juanmb/SkyPointer/python/sky_pointer/pointer.py

from math import pi
from pointing_model import PointingModel
from protocol import Protocol, STEPS
from coords import Coords, EqCoords


def _steps2rad(steps):
    p = 2.*(steps % STEPS)/STEPS
    return pi*(p if p <= 1 else p-2)

def _rad2steps(angle):
    a = (angle/2.) % pi
    return STEPS*(a if a <= pi else pi-a)/pi

def steps2rad(a, b):
    return _steps2rad(a), _steps2rad(b)

def rad2steps(a, b):
    return _rad2steps(a), _rad2steps(b)


class Pointer:
    def __init__(self, device='/dev/ttyUSB0', baud=115200):
        self.__hw = Protocol(device, baud)
        self.hid = self.get_id()
        self.calib = self.__get_calib()
        self.__pm = PointingModel(z1=self.calib[0], z2=self.calib[1],
                                  z3=self.calib[2])
        self.target = EqCoords(0, 0)
        self.home()

    def get_id(self):
        return self.__hw.get_id()

    def home(self):
        return self.__hw.home()

    def __get_calib(self):
        return [self.__hw.get_calib(i) for i in range(3)]

    def set_calib(self, calib):
        if len(calib) != 3:
            raise ValueError("Wrong number of calibration values")

        for i, v in enumerate(calib):
            self.__hw.set_calib(i, v)

    def set_ref(self, eq=None, inst=None, t=0):
        self.__pm.set_ref(eq or self.target, inst or self.get_inst_coords(), t)

    def get_refs(self):
        """Return a list of dictionaries, each containing the observation time,
        equatorial and instrumental coordinates of a reference star"""
        eq = self.__pm.eq_refs
        inst = self.__pm.inst_refs
        t = self.__pm.t_refs

        refs = []
        for i in range(self.__pm.get_nrefs()):
            refs.append({'eq': eq[i], 'inst': inst[i], 't': t[i]})
        return refs

    def steps(self, ha, el):
        self.__hw.move(ha, el)

    def run(self, ha_dir, el_dir):
        if not -1 <= ha_dir <= 1:
            raise ValueError("ha_dir must be between -1 and 1")
        if not -1 <= el_dir <= 1:
            raise ValueError("el_dir must be between -1 and 1")
        half = STEPS/2 - 1
        self.__hw.move(ha_dir*half, el_dir*half)

    def stop(self):
        self.__hw.stop()

    def enable_laser(self, enable):
        self.__hw.enable_laser(enable)

    def get_coords(self):
        return self.__pm.inst_to_eq(steps2rad(*self.__hw.get_pos()))

    def get_inst_coords(self):
        return Coords(*steps2rad(*self.__hw.get_pos()))

    def get_motor_pos(self):
        return self.__hw.get_pos()

    def goto(self, eq):
        self.target = eq
        self.__hw.goto(*rad2steps(*self.__pm.eq_to_inst(eq)))

    def close(self):
        self.__hw.close()
