juanmb/SkyPointer/python/sky_pointer/gui/bright_stars.py

bright_stars = [
    ('Alpha Canis Majoris', 'Sirius', 1.76715, -0.29147),
    ('Alpha Carinae', 'Canopus', 1.67552, -0.91979),
    ('Alpha Centauri', 'Rigil Kentaurus', 3.83972, -1.06116),
    ('Alpha Bootis', 'Arcturus', 3.73500, 0.33510),
    ('Alpha Lyrae', 'Vega', 4.87383, 0.67719),
    ('Alpha Aurigae', 'Capella', 1.38317, 0.80285),
    ('Beta Orionis', 'Rigel', 1.37445, -0.14312),
    ('Alpha Canis Minoris', 'Procyon', 2.00277, 0.09076),
    ('Alpha Eridani', 'Achernar', 0.42761, -0.99833),
    ('Alpha Orionis', 'Betelgeuse', 1.54898, 0.12915),
    ('Beta Centauri', 'Hadar', 3.68264, -1.05418),
    ('Alpha Aquilae', 'Altair', 5.19672, 0.15533),
    ('Alpha Crucis', 'Acrux', 3.25940, -1.10130),
    ('Alpha Tauri', 'Aldebaran', 1.20428, 0.28798),
    ('Alpha Scorpii', 'Antares', 4.31533, -0.46077),
    ('Alpha Virginis', 'Spica', 3.51248, -0.19548),
    ('Beta Geminorum', 'Pollux', 2.02895, 0.48869),
    ('Alpha Piscis Austrini', 'Fomalhaut', 6.01266, -0.51662),
    ('Alpha Cygni', 'Deneb', 5.41488, 0.79063),
    ('Beta Crucis', 'Mimosa', 3.35103, -1.04196),
    ('Alpha Leonis', 'Regulus', 2.65290, 0.20944),
    ('Epsilon Canis Majoris', 'Adhara', 1.82823, -0.50615),
    ('Alpha Geminorum', 'Castor', 1.98531, 0.55676),
    ('Lambda Scorpii', 'Shaula', 4.59894, -0.64752),
    ('Gamma Crucis', 'Gacrux', 3.27686, -0.99658),
    ('Gamma Orionis', 'Bellatrix', 1.41808, 0.10996),
    ('Beta Tauri', 'Elnath', 1.42244, 0.49916),
    ('Beta Carinae', 'Miaplacidus', 2.41292, -1.21649),
    ('Epsilon Orionis', 'Alnilam', 1.46608, -0.02094),
    ('Alpha Gruis', 'Alnair', 5.79449, -0.82030),
    ('Zeta Orionis', 'Alnitak', 1.48789, -0.03316),
    ('Epsilon Ursae Majoris', 'Alioth', 3.37721, 0.97738),
    ('Alpha Persei', 'Mirfak', 0.89012, 0.87092),
    ('Alpha Ursae Majoris', 'Dubhe', 2.89725, 1.07861),
    ('Gamma Velorum', 'Regor', 2.13803, -0.82554),
    ('Delta Canis Majoris', 'Wezen', 1.86750, -0.46077),
    ('Epsilon Sagittarii', 'Kaus Australis', 4.81711, -0.60039),
    ('Eta Ursae Majoris', 'Alkaid', 3.61283, 0.86045),
    ('Theta Scorpii', 'Sargas', 4.61203, -0.75049),
    ('Epsilon Carinae', 'Avior', 2.19475, -1.03847),
    ('Beta Aurigae', 'Menkalinan', 1.57080, 0.78365),
    ('Alpha Trianguli Australis', 'Atria', 4.40259, -1.20428),
    ('Gamma Geminorum', 'Alhena', 1.73660, 0.28623),
    ('Alpha Pavonis', 'Peacock', 5.34943, -0.98960),
    ('Delta Velorum', 'Koo She', 2.29074, -0.95470),
    ('Beta Canis Majoris', 'Mirzam', 1.67115, -0.31416),
    ('Alpha Hydrae', 'Alphard', 2.47837, -0.15184),
    ('Alpha Ursae Minoris', 'Polaris', 0.66323, 1.55858),
    ('Gamma Leonis', 'Algieba', 2.70526, 0.34558),
    ('Alpha Arietis', 'Hamal', 0.55414, 0.41015),
    ('Beta Ceti', 'Diphda', 0.19199, -0.31416),
    ('Sigma Sagittarii', 'Nunki', 4.95237, -0.45902),
    ('Theta Centauri', 'Menkent', 3.69573, -0.63530),
    ('Alpha Andromedae', 'Alpheratz', 0.03491, 0.50789),
    ('Beta Andromedae', 'Mirach', 0.30543, 0.62134),
    ('Kappa Orionis', 'Saiph', 1.51844, -0.16930),
    ('Beta Ursae Minoris', 'Kochab', 3.88772, 1.29503),
    ('Beta Gruis', 'Al Dhanab', 5.94721, -0.81856),
    ('Alpha Ophiuchi', 'Rasalhague', 4.60331, 0.21991),
    ('Beta Persei', 'Algol', 0.82030, 0.71558),
    ('Gamma Andromedae', 'Almach', 0.54105, 0.73827),
    ('Beta Leonis', 'Denebola', 3.09360, 0.25482),
    ('Gamma Cassiopeiae', 'Cih', 0.24871, 1.05941),
    ('Gamma Centauri', 'Muhlifain', 3.32485, -0.85521),
    ('Zeta Puppis', 'Naos', 2.11185, -0.69813),
    ('Iota Carinae', 'Aspidiske', 2.43037, -1.03498),
    ('Alpha Coronae Borealis', 'Alphecca', 4.07971, 0.46600),
    ('Lambda Velorum', 'Suhail', 2.39110, -0.75747),
    ('Zeta Ursae Majoris', 'Mizar', 3.50811, 0.95819),
    ('Gamma Cygni', 'Sadr', 5.33198, 0.70337),
    ('Alpha Cassiopeiae', 'Schedar', 0.17890, 0.98611),
    ('Gamma Draconis', 'Eltanin', 4.69930, 0.89884),
    ('Delta Orionis', 'Mintaka', 1.44862, -0.00524),
    ('Beta Cassiopeiae', 'Caph', 0.03927, 1.03323),
    ('Epsilon Centauri', '', 3.57792, -0.93375),
    ('Delta Scorpii', 'Dschubba', 4.18879, -0.39444),
    ('Epsilon Scorpii', 'Wei', 4.40696, -0.59865),
    ('Alpha Lupi', 'Men', 3.84845, -0.82729),
    ('Eta Centauri', '', 3.82227, -0.73653),
    ('Beta Ursae Majoris', 'Merak', 2.88852, 0.98437),
    ('Epsilon Bootis', 'Izar', 3.86154, 0.47298),
    ('Epsilon Pegasi', 'Enif', 5.68977, 0.17279),
    ('Kappa Scorpii', 'Girtab', 4.63385, -0.68068),
    ('Alpha Phoenicis', 'Ankaa', 0.11345, -0.73827),
    ('Gamma Ursae Majoris', 'Phecda', 3.11541, 0.93724),
    ('Eta Ophiuchi', 'Sabik', 4.49422, -0.27402),
    ('Beta Pegasi', 'Scheat', 6.03884, 0.49044),
    ('Eta Canis Majoris', 'Aludra', 1.93732, -0.51138),
    ('Alpha Cephei', 'Alderamin', 5.58069, 1.09258),
    ('Kappa Velorum', 'Markeb', 2.45219, -0.95993),
    ('Epsilon Cygni', 'Gienah', 5.43670, 0.59341),
    ('Alpha Pegasi', 'Markab', 6.04320, 0.26529),
    ('Alpha Ceti', 'Menkar', 0.79412, 0.07156),
    ('Zeta Ophiuchi', 'Han', 4.35023, -0.18500),
    ('Zeta Centauri', 'Al Nair al Kent.', 3.64774, -0.82554),
    ('Delta Leonis', 'Zosma', 2.94088, 0.35779),
    ('Beta Scorpii', 'Graffias', 4.21061, -0.34558),
    ('Alpha Leporis', 'Arneb', 1.45299, -0.31067),
    ('Delta Centauri', '', 3.17650, -0.88488),
    ('Gamma Corvi', 'Gienah Ghurab', 3.21141, -0.30543),
    ('Zeta Sagittarii', 'Ascella', 4.98728, -0.52185),
    ('Beta Librae', 'Zubeneschamali', 4.00117, -0.16406),
    ('Alpha Serpentis', 'Unukalhai', 4.11898, 0.11170),
    ('Beta Arietis', 'Sheratan', 0.50178, 0.36303),
    ('Alpha Librae', 'Zubenelgenubi', 3.88772, -0.27925),
    ('Alpha Columbae', 'Phact', 1.48353, -0.59516),
    ('Theta Aurigae', '', 1.57080, 0.64926),
    ('Beta Corvi', 'Kraz', 3.28995, -0.40841),
    ('Delta Cassiopeiae', 'Ruchbah', 0.37525, 1.05069),
    ('Eta Bootis', 'Muphrid', 3.64337, 0.32114),
    ('Beta Lupi', 'Ke Kouan', 3.92263, -0.75224),
    ('Iota Aurigae', 'Hassaleh', 1.29591, 0.57945),
    ('Mu Velorum', '', 2.82307, -0.86219),
    ('Alpha Muscae', '', 3.30304, -1.20602),
    ('Upsilon Scorpii', 'Lesath', 4.58585, -0.65101),
    ('Pi Puppis', '', 1.90677, -0.64752),
    ('Delta Sagittarii', 'Kaus Meridionalis', 4.80402, -0.52011),
    ('Gamma Aquilae', 'Tarazed', 5.17490, 0.18500),
    ('Delta Ophiuchi', 'Yed Prior', 4.24988, -0.06458),
    ('Eta Draconis', 'Aldhibain', 4.29351, 1.07338),
    ('Theta Carinae', '', 2.80562, -1.12399),
    ('Gamma Virginis', 'Porrima', 3.32485, -0.02618),
    ('Iota Orionis', 'Hatysa', 1.46171, -0.10297),
    ('Iota Centauri', '', 3.49502, -0.64054),
    ('Beta Ophiuchi', 'Cebalrai', 4.63821, 0.08029),
    ('Beta Eridani', 'Kursa', 1.34390, -0.08901),
    ('Beta Herculis', 'Kornephoros', 4.31969, 0.37525),
    ('Delta Crucis', '', 3.20704, -1.02451),
    ('Beta Draconis', 'Rastaban', 4.58149, 0.91281),
    ('Alpha Canum Venaticorum', 'Cor Caroli', 3.38594, 0.66846),
    ('Gamma Lupi', '', 4.07971, -0.71908),
    ('Beta Leporis', 'Nihal', 1.43117, -0.36303),
    ('Zeta Herculis', 'Rutilicus', 4.36769, 0.55152),
    ('Beta Hydri', '', 0.11345, -1.34914),
    ('Tau Scorpii', '', 4.34587, -0.49218),
    ('Lambda Sagittarii', 'Kaus Borealis', 4.83456, -0.44331),
    ('Gamma Pegasi', 'Algenib', 0.05672, 0.26529),
    ('Rho Puppis', 'Turais', 2.12930, -0.42412),
    ('Beta Trianguli Australis', '', 4.16697, -1.10654),
    ('Zeta Persei', '', 1.02102, 0.55676),
    ('Beta Arae', '', 4.55967, -0.96866),
    ('Alpha Arae', 'Choo', 4.59022, -0.87092),
    ('Eta Tauri', 'Alcyone', 0.99047, 0.42062),
    ('Epsilon Virginis', 'Vindemiatrix', 3.41212, 0.19199),
    ('Delta Capricorni', 'Deneb Algedi', 5.70286, -0.28100),
    ('Alpha Hydri', 'Head of Hydrus', 0.51924, -1.07512),
    ('Delta Cygni', '', 5.17054, 0.78714),
    ('Mu Geminorum', 'Tejat', 1.67115, 0.39270),
    ('Gamma Trianguli Australis', '', 4.00989, -1.19904),
    ('Alpha Tucanae', '', 5.84249, -1.05243),
    ('Theta Eridani', 'Acamar', 0.77667, -0.70337),
    ('Pi Sagittarii', 'Albaldah', 5.01782, -0.36652),
    ('Beta Canis Minoris', 'Gomeisa', 1.95041, 0.14486),
    ('Pi Scorpii', '', 4.18443, -0.45553),
    ('Epsilon Persei', '', 1.03847, 0.69813),
    ('Sigma Scorpii', 'Alniyat', 4.28042, -0.44680),
    ('Beta Cygni', 'Albireo', 5.10945, 0.48869),
    ('Beta Aquarii', 'Sadalsuud', 5.63741, -0.09774),
    ('Gamma Persei', '', 0.80721, 0.93375),
    ('Upsilon Carinae', '', 2.56127, -1.13621),
    ('Eta Pegasi', 'Matar', 5.94721, 0.52709),
    ('Tau Puppis', '', 1.78896, -0.88314),
    ('Delta Corvi', 'Algorel', 3.27249, -0.28798),
    ('Alpha Aquarii', 'Sadalmelik', 5.78577, -0.00524),
    ('Gamma Eridani', 'Zaurak', 1.03847, -0.23562),
    ('Zeta Tauri', 'Alheka', 1.47480, 0.36826),
    ('Epsilon Leonis', 'Ras Elased Austr.', 2.55691, 0.41539),
    ('Gamma Sagittarii', 'Alnasl', 4.73857, -0.53058),
    ('Gamma Hydrae', '', 3.48630, -0.40492),
    ('Iota Scorpii', '', 4.66003, -0.69988),
    ('Zeta Aquilae', 'Deneb el Okab', 4.99600, 0.24260),
    ('Beta Trianguli', '', 0.56723, 0.61087),
    ('Psi Ursae Majoris', '', 2.92343, 0.77667),
    ('Gamma Ursae Minoris', 'Pherkad Major', 4.01862, 1.25315),
    ('Mu Scorpii', '', 4.41568, -0.66323),
    ('Gamma Gruis', '', 5.73341, -0.65275),
    ('Delta Persei', '', 0.97302, 0.83427),
    ('Zeta Canis Majoris', 'Phurad', 1.65806, -0.52534),
    ('Omicron Canis Majoris', '', 1.84569, -0.41539),
    ('Epsilon Corvi', 'Minkar', 3.18523, -0.39444),
    ('Epsilon Aurigae', 'Almaaz', 1.31772, 0.76445),
    ('Beta Muscae', '', 3.34231, -1.18857),
    ('Gamma Bootis', 'Seginus', 3.80482, 0.66846),
    ('Beta Capricorni', 'Dabih', 5.32762, -0.25831),
    ('Epsilon Geminorum', 'Mebsuta', 1.76278, 0.43808),
    ('Mu Ursae Majoris', 'Tania Australis', 2.71399, 0.72431),
    ('Delta Draconis', 'Tais', 5.03091, 1.18159),
    ('Eta Sagittarii', '', 4.79093, -0.64228),
    ('Zeta Hydrae', '', 2.33438, 0.10297),
    ('Nu Hydrae', '', 2.83616, -0.28274),
    ('Lambda Centauri', '', 3.03687, -1.09956),
    ('Alpha Indi', 'Persian', 5.40179, -0.82554),
    ('Beta Columbae', 'Wazn', 1.53153, -0.62483),
    ('Iota Ursae Majoris', 'Talita', 2.35183, 0.83776),
    ('Zeta Arae', '', 4.44623, -0.97738),
    ('Delta Herculis', 'Sarin', 4.51604, 0.43284),
    ('Kappa Centauri', 'Ke Kwan', 3.92263, -0.73478),
    ('Alpha Lyncis', '', 2.44782, 0.60039),
    ('N Velorum', '', 2.49146, -0.99484),
    ('Pi Herculis', '', 4.51604, 0.64228),
    ('Nu Puppis', '', 1.73660, -0.75398),
    ('Theta Ursae Majoris', 'Al Haud', 2.50018, 0.90234),
    ('Zeta Draconis', 'Aldhibah', 4.48986, 1.14668),
    ('Phi Sagittarii', '', 4.91310, -0.47124),
    ('Eta Aurigae', 'Hoedus II', 1.33954, 0.71908),
    ('Alpha Circini', '', 3.85281, -1.13446),
    ('Pi Orionis', 'Tabit', 1.26536, 0.12217),
    ('Epsilon Leporis', '', 1.33081, -0.39095),
    ('Kappa Ophiuchi', '', 4.44186, 0.16406),
    ('G Scorpii', '', 4.66876, -0.64577),
    ('Zeta Cygni', '', 5.55451, 0.52709),
    ('Gamma Cephei', 'Errai', 6.19156, 1.35438),
    ('Delta Lupi', '', 4.01862, -0.70860),
    ('Epsilon Ophiuchi', 'Yed Posterior', 4.26733, -0.08203),
    ('Eta Serpentis', 'Alava', 4.80402, -0.05061),
    ('Beta Cephei', 'Alphirk', 5.62432, 1.23220),
    ('Alpha Pictoris', '', 1.78024, -1.08036),
    ('Theta Aquilae', '', 5.28398, -0.01396),
    ('Sigma Puppis', '', 1.95913, -0.75573),
    ('Pi Hydrae', '', 3.69137, -0.46600),
    ('Sigma Librae', 'Brachium', 3.94444, -0.44157),
    ('Gamma Lyrae', 'Sulaphat', 4.96983, 0.57072),
    ('Gamma Hydri', '', 0.99047, -1.29503),
    ('Delta Andromedae', '', 0.17017, 0.53931),
    ('Theta Ophiuchi', '', 4.54658, -0.43633),
    ('Delta Aquarii', 'Skat', 5.99957, -0.27576),
    ('Mu Leporis', '', 1.36572, -0.28274),
    ('Omega Carinae', '', 2.67908, -1.22173),
    ('Iota Draconis', 'Edasich', 4.03607, 1.02974),
    ('Alpha Doradus', '', 1.19555, -0.95993),
    ('p Carinae', '', 2.75762, -1.07687),
    ('Mu Centauri', '', 3.62156, -0.74176),
    ('Eta Geminorum', 'Propus', 1.63625, 0.39270),
    ('Alpha Herculis', 'Rasalgethi', 4.51604, 0.25133),
    ('Gamma Arae', '', 4.55967, -0.98437),
    ('Beta Phoenicis', '', 0.28798, -0.81507),
    ('Rho Persei', 'Gorgonea Tertia', 0.80721, 0.67719),
    ('Delta Ursae Majoris', 'Megrez', 3.20704, 0.99484),
    ('Eta Scorpii', '', 4.50295, -0.75398),
    ('Nu Ophiuchi', '', 4.70803, -0.17104),
    ('Tau Sagittarii', '', 5.00473, -0.48346),
    ('Alpha Reticuli', '', 1.10828, -1.09083),
    ('Theta Leonis', 'Chort', 2.94088, 0.26878),
    ('Xi Puppis', 'Asmidiske', 2.04640, -0.43459),
    ('Epsilon Cassiopeiae', 'Segin', 0.49742, 1.11177),
    ('Eta Orionis', 'Algjebbah', 1.41372, -0.04189),
    ('Xi Geminorum', 'Alzirr', 1.76715, 0.22515),
    ('Omicron Ursae Majoris', 'Muscida', 2.22529, 1.05941),
    ('Delta Aquilae', '', 5.08327, 0.05411),
    ('Epsilon Lupi', '', 4.02735, -0.78016),
    ('Zeta Virginis', 'Heze', 3.55611, -0.01047),
    ('Epsilon Hydrae', '', 2.29947, 0.11170),
    ('Lambda Orionis', 'Meissa', 1.46171, 0.17279),
    ('q Carinae', '', 2.69217, -1.06989),
    ('Delta Virginis', 'Auva', 3.38594, 0.05934),
    ('Zeta Cephei', '', 5.80758, 1.01578),
    ('Theta Tauri', '', 1.17373, 0.27751),
    ('Gamma Phoenicis', '', 0.38397, -0.75573),
    ('Lambda Tauri', '', 1.05156, 0.21817),
    ('Nu Centauri', '', 3.62156, -0.72780),
    ('Zeta Lupi', '', 3.97935, -0.90932),
    ('Eta Cephei', '', 5.43234, 1.07861),
    ('Zeta Pegasi', 'Homam', 5.93848, 0.18850),
    ('Alpha Trianguli', 'Mothallah', 0.49306, 0.51662),
    ('Eta Lupi', '', 4.18879, -0.67021),
    ('Mu Herculis', '', 4.65130, 0.48346),
    ('Beta Pavonis', '', 5.43234, -1.15541),
    ('a Carinae', '', 2.40419, -1.02800),
    ('Zeta Leonis', 'Adhafera', 2.69217, 0.40841),
    ('Lambda Aquilae', 'Althalimain', 5.00037, -0.08552),
    ('Lambda Ursae Majoris', 'Tania Borealis', 2.69217, 0.74875),
    ('Beta Lyrae', 'Sheliak', 4.93056, 0.58294),
    ('Eta Cassiopeiae', 'Achird', 0.21380, 1.00880),
    ('Eta Ceti', 'Dheneb', 0.30107, -0.17802),
    ('Chi Carinae', '', 2.08131, -0.92502),
    ('Delta Bootis', '', 3.99680, 0.58119),
    ('Gamma Ceti', 'Kaffaljidhma', 0.71122, 0.05585),
    ('Eta Leonis', '', 2.64854, 0.29322),
    ('Eta Herculis', '', 4.37641, 0.67893),
    ('Tau Ceti', '', 0.45379, -0.27751),
    ('Sigma Canis Majoris', '', 1.84132, -0.48695),
    ('Nu Ursae Majoris', 'Alula Borealis', 2.95833, 0.57770),
    ('Beta Bootis', 'Nekkar', 3.93572, 0.70511),
    ('Alpha Telescopii', '', 4.83020, -0.80285),
    ('Epsilon Gruis', '', 5.97339, -0.89535),
    ('Kappa Canis Majoris', '', 1.78896, -0.56723),
    ('Delta Geminorum', 'Wasat', 1.91986, 0.38397),
    ('Iota Cephei', '', 5.97775, 1.15541),
    ('Gamma Sagittae', '', 5.23162, 0.34034),
    ('Mu Pegasi', 'Sadalbari', 5.97775, 0.42935),
    ('Delta Eridani', 'Rana', 0.97302, -0.17104),
    ('Omicron Leonis', 'Subra', 2.53509, 0.17279),
    ('Phi Velorum', 'Tseen Ke', 2.60490, -0.95295),
    ('Xi Sagittarii', '', 4.96546, -0.36826),
    ('Theta Pegasi', 'Baham', 5.80322, 0.10821),
    ('Epsilon Tauri', 'Ain', 1.17373, 0.33510),
    ('Beta Cancri', 'Tarf', 2.16857, 0.16057),
    ('Xi Hydrae', '', 3.02378, -0.55676),
    ('Mu Serpentis', '', 4.14516, -0.05934),
    ('Xi Serpentis', '', 4.61640, -0.26878),
]
